rvbcrs/PoolLab/designs/TB6612.step

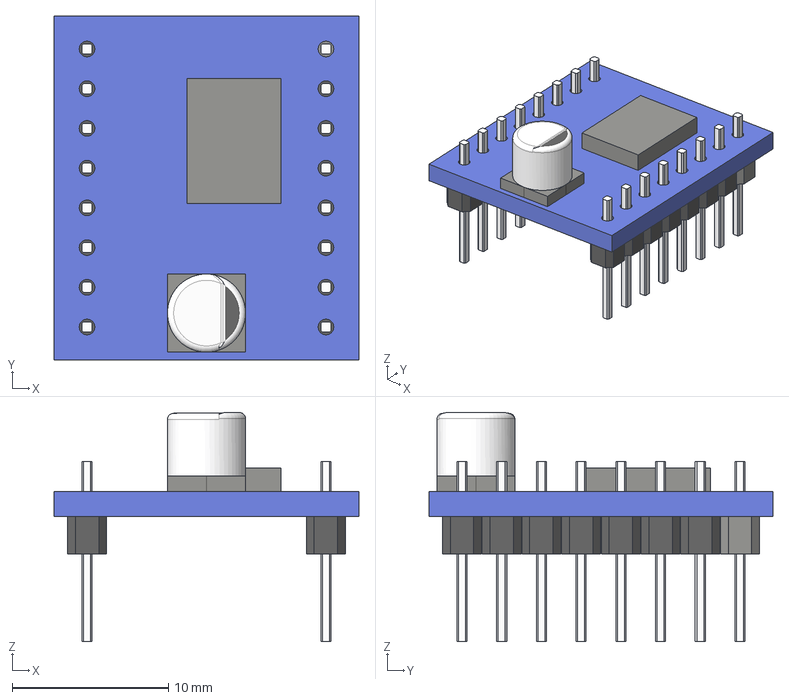
[picture p15: CAD file, 2026-02-06]
designs/TB6612.step
19.5 x 22.0 x 14.7 mm
