rvbcrs/PoolLab/designs/LM2596.stp

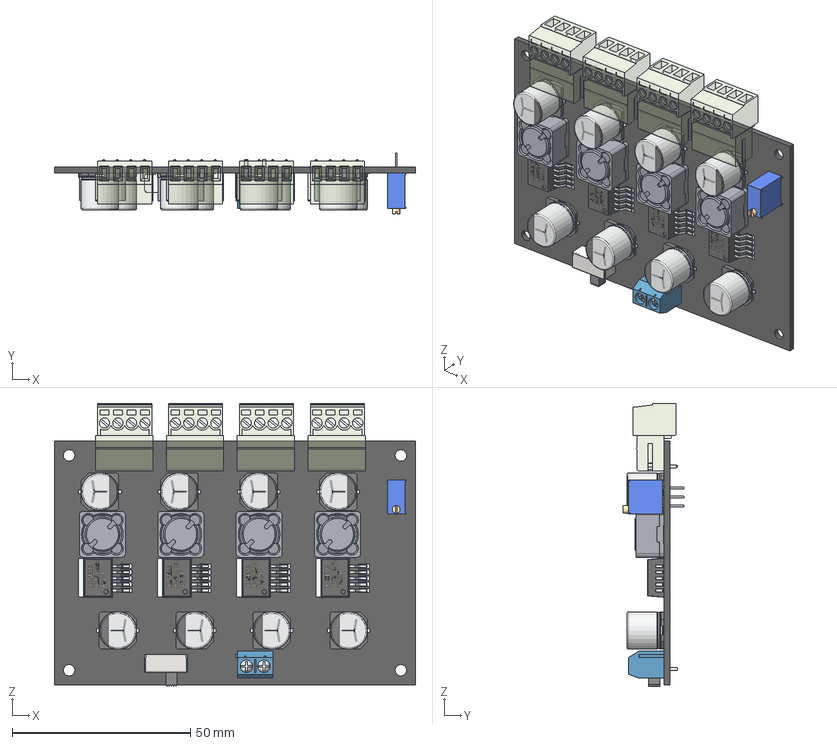
[picture p16: CAD file, 2026-02-06]
designs/LM2596.stp
101.3 x 17.2 x 79.5 mm
PCB
Female Connector x 4
Male Connector x 4
Input Connector
CAPAE-D10.0x10.2 x 8
SMD Unidentified x 4
SRR1208 x 4
拨动开关
TRIMER_POT
